swrraab/WRO---FE---2025/models/Camera Mount Extension.png

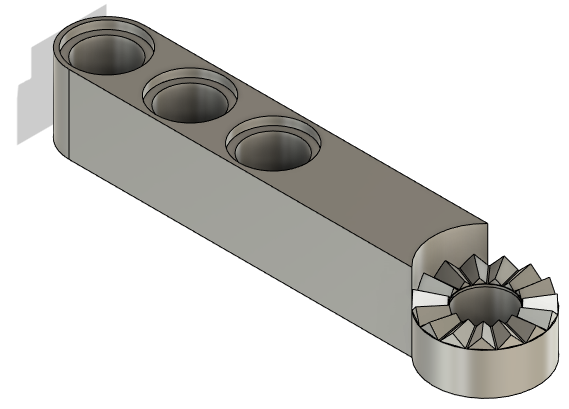
models/Camera Mount Extension.png
