swrraab/WRO---FE---2025/v-photos/Top View.png

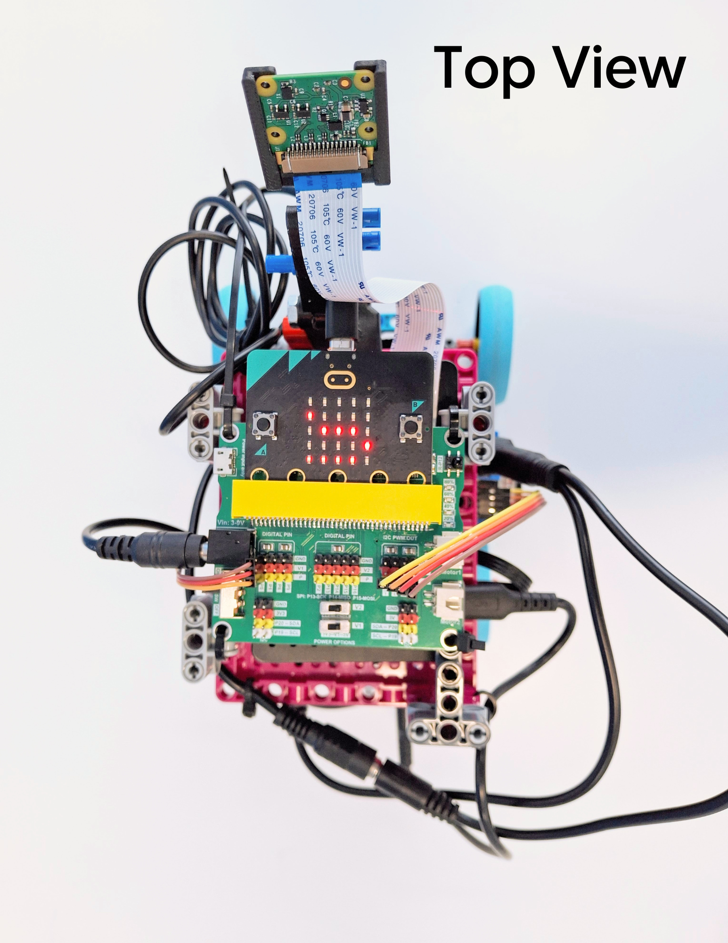
v-photos/Top View.png
